kadyrbai1/computer-graphic/IO_Watch/CAD/Scad/MainBody.scad

import("./imports/MainBody.stl");
