kadyrbai1/computer-graphic/IO_Watch/CAD/Scad/OuterGlassRing.scad

import("./imports/OuterGlassRing.stl");
